adamforbes92/FISCuntrolCAN/Code/FISCAN_config.h

/* for defining all used variables, libraries, etc.
*/
#include <SPI.h>        // for FIS display
#include <TLBFISLib.h>  // for FIS display

#include <KLineKWP1281Lib.h>  // for k-line diag (external to this proj.)

#include <ESP32_CAN.h>  // for CAN

#include "OneButton.h"  // for monitoring the stalk buttons - it's easier to use a lib. than parse each loop - and it counts hold presses
#include <TickTwo.h>    // for repeated tasks

// for OTA
#include <AsyncTCP.h>
#include <ESPAsyncWebServer.h>
#include <ESPAsyncHTTPUpdateServer.h>
#include <WiFi.h>            // included for WiFi pages
#include <ESPmDNS.h>         // included for WiFi pages

#define serialDebug 0      // if 1, will Serial print
#define serialBaud 115200  // define Serial talkback baud rate
#define ChassisCANDebug 0  // if 1, will print CAN 1 (Chassis) messages
#define checkLED 0         // 0 = off, 1 = do LED check (for debug ONLY, disable on release)

#ifdef serialDebug
#define DEBUG_PRINT(x) Serial.print(x)
#define DEBUG_PRINTLN(x) Serial.println(x)
#define DEBUG_PRINTF(x...) Serial.printf(x)
#else
#define DEBUG_PRINT(x)
#define DEBUG_PRINTLN(x)
#define DEBUG_PRINTF(x...)
#endif

#define wifiHostName "FISCuntrolCAN"  // the WiFi name

#define hasFIS 1                             // toggle for FIS display
#define fisWakeDelay 500                     // delay to let FIS cluster boot, if data sent immediately it doesn't boot(!)
#define globalTextAlignment TLBFISLib::LEFT  // TLBFISLib::LEFT / CENTER / RIGHT - note spelling(!)
#define showBootScreen 2                     // 0 = off, 1 = Welcome message, 2 = Custom Logo
#define bootScreenDuration 4000              // boot logo duration
#define connectionDelayDuration 0            // 'connecting...' information duration
#define displayECUonBoot 0                   // display ECU Part Number etc when connected

#define hasK 0            // use K-line for diag
#define hasCAN 1          // use CAN for diag - needs a lot of work!  What variables do we want to see?
#define hasHaldex 1       // has OpenHaldex
#define hasRTC 0          // has RTC for time control.  Removed to save space - incorporate ESP RTC / WiFi get time lastminuteengineers.com/esp32-ntp-server-date-time-tutorial/
#define isMPH 1           // convert kmh readings into mph
#define mphFactor 621371  // to convert from kmh > mph
#define logFrequency 100  // logs Per Second

#define ignitionMonitorPin 35  // for monitoring ignition signal via. optocoupler
#define K_TX 17                // TX pin for K-line (MC33290)
#define K_RX 16                // RX pin for K-line (MC33290)
#define K_line Serial2         // use Serial2 as the K-line port
#define K_Baud 10400           // define module baud rate (ME7.x = 10400)
#define K_Module 0x01          // define address connection.  Could be adjusted to connect to other modules, but who cares?!

#define pinCAN_RX 13  // RX pin for SN65HVD230 (CAN_RX)
#define pinCAN_TX 14  // TX pin for SN65HVD230 (CAN_TX)

#define fisCLK 18                         // FIS Clock Output - these are default CLK for ESP32
#define fisDATA 23                        // FIS Data Output - these are default MOSI for ESP32
#define fisENA 19                         // FIS Enable Output - required, but set to 19 (chip select) for ESP32
#define screenSize TLBFISLib::FULLSCREEN  // use the full screen for the FIS
//#define screenSize TLBFISLib::HALFSCREEN                         // use the half screen (bottom half) for the FIS kept for completeness
#define SPI_INSTANCE SPI  // SPI interface for FIS

#define stalkPushUp 34           // input stalk UP
#define stalkPushDown 39         // input stalk DOWN
#define stalkPushReset 36        // input stalk RESET
#define stalkPushUpReturn 27     // if FIS disable - use this to match stalk UP
#define stalkPushDownReturn 26   // if FIS disable - use this to match stalk DOWN
#define stalkPushResetReturn 25  // if FIS disable - use this to match stalk RESET

#define deviceName "FISCuntrol"  // for ESP32 Bluetooth name - so that it's visible on other devices
#define appMessageStatus 1       // OpenHaldex Message Status
#define canRefresh 50            // send CAN updates every xx ms

#define arraySize(array) (sizeof((array)) / sizeof((array)[0]))  // generic array size calculator, handy to have
#define serialPacketEnd 0xFF                                     // define Bluetooth Serial Packet end

#define MOTOR1_ID 0x280
#define MOTOR2_ID 0x288
#define MOTOR3_ID 0x380
#define MOTOR5_ID 0x480
#define MOTOR6_ID 0x488
#define MOTOR7_ID 0x588
#define MOTOR_FLEX_ID 0x580
#define GRA_ID 0x38A
#define BRAKES1_ID 0x1A0
#define BRAKES2_ID 0x2A0
#define BRAKES3_ID 0x4A0
#define BRAKES5_ID 0x5A0
#define HALDEX_ID 0x2C0
#define fisCuntrol_ID 0x6A0  // FIS CAN Address
#define openHaldex_ID 0x6B0  // OpenHaldex CAN Address
#define ignitron1_ID 0x7C4
#define ignitron2_ID 0x7C6
#define ignitron3_ID 0x7C8

// Haldex mode types
typedef enum openhaldex_mode_id {
  MODE_STOCK,
  MODE_FWD,
  MODE_5050,
  MODE_6040,
  MODE_7525,
  MODE_CUSTOM,
} openhaldex_mode_id;

typedef struct openhaldexState {
  openhaldex_mode_id mode;
  byte ped_threshold;
  bool mode_override;
} openhaldexState;

extern char* connectingToK = "Connecting...";
extern char* connectedToK = "Connected...";

extern char* connectingToCAN = "Connecting...";
extern char* connectedToCAN = "Connected...";

extern char* haldexOptions[] = { "OpenHaldex", "Stock", "FWD", "5050", "7525" };
extern char* connectingToOpenHaldex = "Connecting...";
extern char* connectedToOpenHaldex = "Connected...";

extern bool ignitionState = false;         // variable for reading the ignition pin status
extern bool ignitionStateRunOnce = false;  // variable for reading the first run loop
extern bool fisDisable = false;            // is the FIS turned off?
extern bool fisBeenToggled = false;        // been toggled on/off?  Don't display welcome if!
extern bool btConnected = false;           // is the Bluetooth connected?
extern bool runOnce = false;               // for launching boot LCD/FIS
extern bool showHaldex = false;            // for displaying Haldex options instead of data
extern bool isConnectedK = false;          // for monitoring k-line connection
extern bool isConnectedCAN = false;        // for monitoring CAN connection
extern bool hasOpenHaldex = false;         // visbility of OpenHaldex via. CAN
extern bool mimickSet = false;             // can't change FIS screen etc in interrupts, so set a flag to catch in the next loop
extern bool triggerShutdown = true;
extern bool isStandalone = false;

extern uint8_t vehicleSpeed = 0;
extern uint8_t haldexVehicleSpeed = 0;
extern uint8_t haldexEngagement = 0;
extern uint8_t haldexState = 0;
extern uint8_t lockTarget = 0;
extern uint8_t pedValue = 0;
extern int boardSoftwareVersion = 0;
extern uint32_t lastTransmission = 0;
extern uint8_t lastMode = 0;
extern int lastBlock = -1;
extern int lastHaldex = -1;
extern unsigned long lastDataRetrieve = 0;  // for checking if it's time to get more data...

extern uint16_t vehicleRPM = 0;  // current RPM
extern bool vehicleEML = false;  // current EML light status
extern bool vehicleEPC = false;  // current EPC light status
extern int calcSpeed = 0;        // temp var for calculating speed

extern void setupWiFi();
extern void setupOTA();

byte btIncoming[10];
byte btOutgoing[4];
int incomingLen;

extern String fisLine[8] = { "" };

struct card1 {
  char variableName[0x0F];
  int variablePos;
  int FISline;
};

struct card2 {
  char variableName[0x0F];
  int variablePos;
  int FISline;
};

struct card3 {
  char variableName[0x0F];
  int variablePos;
  int FISline;
};

struct card4 {
  char variableName[0x0F];
  int variablePos;
  int FISline;
};

struct card5 {
  char variableName[0x0F];
  int variablePos;
  int FISline;
};

struct card1 card1[7];  // 7 entries for each FIS line
struct card2 card2[7];  // 7 entries for each FIS line
struct card3 card3[7];  // 7 entries for each FIS line
struct card4 card4[7];  // 7 entries for each FIS line
struct card5 card5[7];  // 7 entries for each FIS line

// Enable/disable printing library debug information on the Serial Monitor.
#define debug_info false  // You may change the debug level in "KLineKWP1281Lib.h".
// Select whether or not your serial interface can receive at the same time as sending (or whether or not your K-line interface has echo as it should).
// Most software serial libraries for AVR microcontrollers are half-duplex (can't receive while sending), so if using such library this should be false.
#define is_full_duplex true

// Initialize the serial port
void beginFunction(unsigned long baud) {
  K_line.begin(K_Baud, SERIAL_8N1, K_RX, K_TX);
}

// Stop communication on the serial port
void endFunction() {
  K_line.end();
}

// Send a byte
void sendFunction(uint8_t data) {
  K_line.write(data);
}

// Receive a byte
bool receiveFunction(uint8_t* data) {
  if (K_line.available()) {
    *data = K_line.read();
    return true;
  }
  return false;
}

// GRAPHICS
extern const unsigned char avant[] PROGMEM = {
  0x07, 0xfe, 0x00, 0x3f, 0xff, 0xc0, 0x78, 0x01, 0xe0, 0xc8, 0x01, 0x30, 0xb4, 0x02, 0xd0, 0xc4, 0x02, 0x30, 0x84, 0x02, 0x10, 0x84, 0x02, 0x10, 0x84, 0x02, 0x10, 0x84, 0x02, 0x10, 0x84, 0x02, 0x10, 0x9f, 0xff, 0x90, 0xb0, 0x00, 0xd0, 0xe0, 0x00, 0x70, 0x80, 0x00, 0x10, 0x80, 0x00, 0x10, 0x80, 0x00, 0x10, 0xe0, 0x00, 0x70, 0xb7, 0xfe, 0xd0, 0x98, 0x01, 0x90, 0x90, 0x00, 0x90, 0x90, 0x00, 0x90, 0x90, 0x00, 0x90, 0x90, 0x00, 0x90, 0x90, 0x00, 0x90, 0xf0, 0x00, 0xf0, 0x90, 0x00, 0x90, 0x90, 0x00, 0x90, 0x90, 0x00, 0x90, 0x90, 0x00, 0x90, 0x90, 0x00, 0x90, 0x90, 0x00, 0x90, 0x90, 0x00, 0x90, 0xb0, 0x00, 0xd0, 0xd0, 0x00, 0xb0, 0x90, 0x00, 0x90, 0x90, 0x00, 0x90, 0x90, 0x00, 0x90, 0x90, 0x00, 0x90, 0x98, 0x01, 0x90, 0x97, 0xfe, 0x90, 0xa0, 0x00, 0x50, 0xe0, 0x00, 0x70, 0x90, 0x00, 0x90, 0x7f, 0xff, 0xe0, 0x1f, 0xff, 0x80
};

extern const unsigned char sedan[] PROGMEM = {
  0x07, 0xfe, 0x00, 0x3f, 0xff, 0xc0, 0x78, 0x01, 0xe0, 0xc8, 0x01, 0x30, 0xb4, 0x02, 0xd0, 0xc4, 0x02, 0x30, 0x84, 0x02, 0x10, 0x84, 0x02, 0x10, 0x84, 0x02, 0x10, 0x84, 0x02, 0x10, 0x84, 0x02, 0x10, 0x9f, 0xff, 0x90, 0xb0, 0x00, 0xd0, 0xe0, 0x00, 0x70, 0x80, 0x00, 0x10, 0x80, 0x00, 0x10, 0x80, 0x00, 0x10, 0xe0, 0x00, 0x70, 0xb7, 0xfe, 0xd0, 0x98, 0x01, 0x90, 0x90, 0x00, 0x90, 0x90, 0x00, 0x90, 0x90, 0x00, 0x90, 0x90, 0x00, 0x90, 0x90, 0x00, 0x90, 0xf0, 0x00, 0xf0, 0x90, 0x00, 0x90, 0x90, 0x00, 0x90, 0x90, 0x00, 0x90, 0x90, 0x00, 0x90, 0x90, 0x00, 0x90, 0x90, 0x00, 0x90, 0x90, 0x00, 0x90, 0xb8, 0x01, 0xd0, 0xe7, 0xfe, 0x70, 0x80, 0x00, 0x10, 0xc0, 0x00, 0x30, 0xa0, 0x00, 0x50, 0x90, 0x00, 0x90, 0x8c, 0x03, 0x10, 0x83, 0xfc, 0x10, 0xc0, 0x00, 0x30, 0x60, 0x00, 0x60, 0x50, 0x00, 0xa0, 0x3f, 0xff, 0xc0, 0x07, 0xfe, 0x00
};

extern const unsigned char left_door[] PROGMEM = {
  0x02, 0x07, 0x0c, 0x18, 0x30, 0x63, 0xc5, 0x79
};

extern const unsigned char right_door[] PROGMEM = {
  0xc0, 0xe0, 0x30, 0x18, 0x0c, 0xc6, 0xa3, 0x9e
};

extern const unsigned char avant_trunc[] PROGMEM = {
  0x40, 0x08, 0xff, 0xfc, 0xff, 0xfc, 0x7f, 0xf8
};

extern const unsigned char sedan_trunc[] PROGMEM = {
  0x80, 0x00, 0x40, 0xc0, 0x00, 0xc0, 0xe0, 0x01, 0xc0, 0xf8, 0x07, 0xc0, 0x7f, 0xff, 0x80, 0x3f, 0xff, 0x00, 0x1f, 0xfe, 0x00
};

extern const unsigned char b5f[] PROGMEM = {
  0x00, 0x00, 0x00, 0x00, 0x00, 0x00, 0x00, 0x00, 0x00, 0x00, 0x00, 0x00, 0x00, 0x00, 0x00, 0x00, 0x00, 0x00, 0x00, 0x00, 0x00, 0x00, 0x00, 0x00, 0x00, 0x00, 0x00, 0x00, 0x00, 0x00, 0x00, 0x00, 0x00, 0x00, 0x00, 0x00, 0x00, 0x00, 0x00, 0x00, 0x1f, 0xff, 0xff, 0xff, 0xff, 0xff, 0xff, 0x80, 0x1f, 0xff, 0xff, 0xff, 0xff, 0xff, 0xff, 0x80, 0x1f, 0xff, 0xf0, 0x00, 0x1f, 0xff, 0xf1, 0x80, 0x1f, 0xff, 0xc0, 0x00, 0x07, 0xff, 0x01, 0x80, 0x1f, 0xff, 0x80, 0x00, 0x03, 0xf0, 0x01, 0x80, 0x1c, 0x0f, 0x80, 0x00, 0x01, 0xe0, 0x01, 0x80, 0x1c, 0x0f, 0x00, 0x00, 0x00, 0xe0, 0x01, 0x80, 0x1c, 0x0f, 0x00, 0x00, 0x00, 0xe0, 0x07, 0x80, 0x1c, 0x0e, 0x00, 0x00, 0x00, 0xe0, 0xc7, 0x80, 0x1c, 0x0e, 0x00, 0x00, 0x00, 0x60, 0x03, 0x80, 0x1c, 0x0e, 0x00, 0x00, 0x00, 0x60, 0x01, 0x80, 0x1c, 0x0e, 0x00, 0x00, 0x00, 0x60, 0x01, 0x80, 0x1c, 0x0e, 0x00, 0x00, 0x00, 0x78, 0x01, 0x80, 0x1c, 0x0e, 0x00, 0x00, 0x00, 0x7f, 0x81, 0x80, 0x1c, 0x0e, 0x00, 0x00, 0x00, 0x3f, 0xff, 0x80, 0x1c, 0x0e, 0x00, 0x00, 0x00, 0x20, 0x03, 0x80, 0x1c, 0x0e, 0x00, 0x00, 0x00, 0x20, 0x01, 0x80, 0x1c, 0x0e, 0x03, 0xff, 0xe0, 0x20, 0x01, 0x80, 0x1c, 0x0e, 0x07, 0xff, 0xf0, 0x20, 0x01, 0x80, 0x1c, 0x0e, 0x07, 0xff, 0xf0, 0x20, 0x01, 0x80, 0x1c, 0x0f, 0x07, 0xff, 0xf0, 0x3f, 0xff, 0x80, 0x1c, 0x0f, 0x07, 0xff, 0xe0, 0x3f, 0xf3, 0x80, 0x1c, 0x0f, 0x81, 0xf0, 0x00, 0x3f, 0xf1, 0x80, 0x1c, 0x00, 0x18, 0xe0, 0x00, 0x3f, 0xf1, 0x80, 0x1f, 0xe0, 0xd6, 0xe0, 0x00, 0x60, 0x01, 0x80, 0x1f, 0xfc, 0xf8, 0xe0, 0x00, 0x60, 0x01, 0x80, 0x1f, 0xfe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
  0xb2, 0xe7, 0xfa, 0x00, 0x00, 0x94, 0x88, 0x00, 0xfe, 0xfc, 0xa8, 0x80, 0x82, 0xa3, 0x88, 0x00,
  0xba, 0x3f, 0xfb, 0x00, 0xba, 0x37, 0xe1, 0x80, 0xba, 0x66, 0x06, 0x80, 0x82, 0xa1, 0x98, 0x80,
  0xfe, 0xf0, 0xe4, 0x80
};
