adamforbes92/FISCuntrolCAN/Code/FISCAN_FIS.ino

void bootFIS() {
  DEBUG_PRINTLN("Booting FIS...");

  delay(fisWakeDelay);
  FIS.errorFunction(custom_error_function);
  FIS.begin();
  FIS.initScreen(screenSize);  // defined in config

  DEBUG_PRINTLN("Booting FIS Complete!");
}

void displayFIS() {
  FIS.update();
  FIS.setTextAlignment(globalTextAlignment);
  FIS.setFont(TLBFISLib::COMPACT);

  if (isConnectedK && !showHaldex) {
    char buf[16];
    sprintf(buf, "BLOCK %d", readBlock);
    FIS.writeText(0, 1, buf);
    FIS.drawLine(0, 9, 64);
  }

  if (showHaldex) {
    FIS.writeText(0, 1, "OPENHALDEX");
    FIS.drawLine(0, 9, 64);

    if (isStandalone) {
      FIS.writeText(0, 2, "STANDALONE!");
      FIS.drawLine(0, 17, 64);
    }
  }

  if (isConnectedCAN && !showHaldex) {
    FIS.writeText(0, 1, "CAN DATA");
    FIS.drawLine(0, 9, 64);
  }

  FIS.setTextAlignment(globalTextAlignment);
  FIS.setFont(TLBFISLib::COMPACT);
  char combinedArray[500];

  for (uint8_t i = 0; i < 8; i++) {
    char buf1[fisLine[i].length() + 1];
    fisLine[i].toUpperCase();
    fisLine[i].toCharArray(buf1, fisLine[i].length() + 1);
    if (i == 0) {
      sprintf(combinedArray, "%s", buf1);  // with word space
    } else {
      sprintf(combinedArray, "%s\n%s", combinedArray, buf1);  // with word space
    }
  }
  //sprintf(combinedArray, "%s", combinedArray, "\n");  // with word space
  DEBUG_PRINTLN(combinedArray);
  FIS.writeMultiLineText(0, 35, combinedArray, false);
}

void drawScreen() {
  //Draw the logo bitmap at position X0, Y2, with its width of 64px and a height of 45px.
  FIS.drawBitmap(0, 0, 64, 88, MK4Golf);

  //Set a workspace in the middle of the FIS and clear it.
  //The size of the QR code is 25x25px, so a rectangle of 27x27px should be cleared "behind it" to make the code readable.
  //FIS.setWorkspace((64 - 27) / 2, (48 - 27) / 2, 27, 27, true);  //"true" = also clear

  //Draw the QR code bitmap at position X1, Y1 (inside the workspace defined above), with its width and height of 25px.
  //FIS.drawBitmap(1, 1, 25, 25, qr);

  //It is not necessary to reset the workspace, because an "error" event will automatically clear all custom workspaces.
}

void custom_error_function(unsigned long duration) {
  //Errors are measured in milliseconds, to offer the possibility of differentiating between events.
  //Here, this value won't be used, so cast it to void to avoid a compiler warning.
  (void)duration;

  //Initialize the screen.
  FIS.initScreen();  //calling without a parameter will default to the halfscreen size

  //Write a message.
  FIS.writeMultiLineText(0, 16, "Error"
                                "\n"
                                "event");  //adjacent strings are concatenated by the compiler
}
