adamforbes92/FISCuntrolCAN/Code/FISCAN_buttons.ino

void setupButtons() {
  stalkUpButton.attachClick(singleClickUp);
  stalkUpButton.attachMultiClick(doubleClickUp);
  stalkUpButton.setPressMs(1000);  // that is the time when LongPressStart is called
  stalkUpButton.attachLongPressStart(pressStartUp);

  stalkDownButton.attachClick(singleClickDown);
  stalkUpButton.attachMultiClick(doubleClickDown);
  stalkDownButton.setPressMs(1000);  // that is the time when LongPressStart is called
  stalkDownButton.attachLongPressStart(pressStartDown);

  stalkResetButton.attachClick(singleClickReset);
  stalkResetButton.setPressMs(1000);  // that is the time when LongPressStart is called
  stalkResetButton.attachLongPressStart(pressStartReset);
}

void mimickStalkButtons() {
  digitalWrite(stalkPushUpReturn, digitalRead(stalkPushUp));
  digitalWrite(stalkPushDownReturn, digitalRead(stalkPushDown));
  digitalWrite(stalkPushResetReturn, digitalRead(stalkPushReset));
}

// this function will be called when the button was pressed 1 time only.
void singleClickUp() {
  Serial.println("pressed up");
  if (!fisDisable) {
    if (showHaldex && hasHaldex) {
      lastMode++;
      if (lastMode > 4) {
        lastMode = 0;
      }
      switch (lastMode) {
        case 0:
          state.mode = MODE_STOCK;
          break;
        case 1:
          state.mode = MODE_FWD;
          break;
        case 2:
          state.mode = MODE_5050;
          break;
        case 3:
          state.mode = MODE_6040;
          break;
        case 4:
          state.mode = MODE_7525;
          break;
      }
    } else {
      readBlock++;
    }
  }
}  // singleClick

void singleClickDown() {
  Serial.println("pressed down");
  if (!fisDisable) {
    if (showHaldex && hasHaldex) {
      lastMode--;
      if (lastMode > 254) {
        lastMode = 4;
      }
      switch (lastMode) {
        case 0:
          state.mode = MODE_STOCK;
          break;
        case 1:
          state.mode = MODE_FWD;
          break;
        case 2:
          state.mode = MODE_5050;
          break;
        case 3:
          state.mode = MODE_6040;
          break;
        case 4:
          state.mode = MODE_7525;
          break;
      }
    } else {
      readBlock--;
    }
  }
}  // singleClick

void doubleClickUp() {
  if (!fisDisable) {
    readBlock = readBlock + 10;
  }
  if (readBlock > 255) {
    readBlock = 1;
  }
}  // singleClick

void doubleClickDown() {
  if (!fisDisable) {
    readBlock = readBlock - 10;
  }
  if (readBlock < 1) {
    readBlock = 255;
  }
}  // singleClick

void singleClickReset() {
  Serial.println("pressed reset");
}  // singleClick

void pressStartUp() {
  if (hasHaldex) {
    lastHaldex = -1;
    lastBlock = 0;
    showHaldex = !showHaldex;
    for (int i = 0; i < 8; i++) {
      fisLine[i] = "";
    }
  }
}  // pressStart()

void pressStartDown() {
  readBlock = 1;
}  // pressStart()

void pressStartReset() {
  fisDisable = !fisDisable;  //flip-flop fisDisable
  mimickSet = true;
}  // pressStart()
