adamforbes92/FISCuntrolCAN/Code/FISCAN_vers.h

/*
> *** Boot logos to be added ***
    *Bitmaps can easily be generated with the https://javl.github.io/image2cpp/ tool.
    *For halfscreen, the max visible size is 64x48, and for fullscreen it is 64x88.
> Revised code and PCBs for smaller footprints
> V1.01 - Added debug statements
> V1.02 - Edited PCB, missing pullup on K-Line (won't connect to ECU if missing!), added 1k pullDOWN on ENA ESP side, added 10k pullUP on ENA cluster side(!)
> V1.03 - Added CAN details, sorted RPM.  Left shift all text.  Confirmed working.
> V1.04 - Added OTA
*/
